StevenMHernandez/pet-bot/network/diagram.png

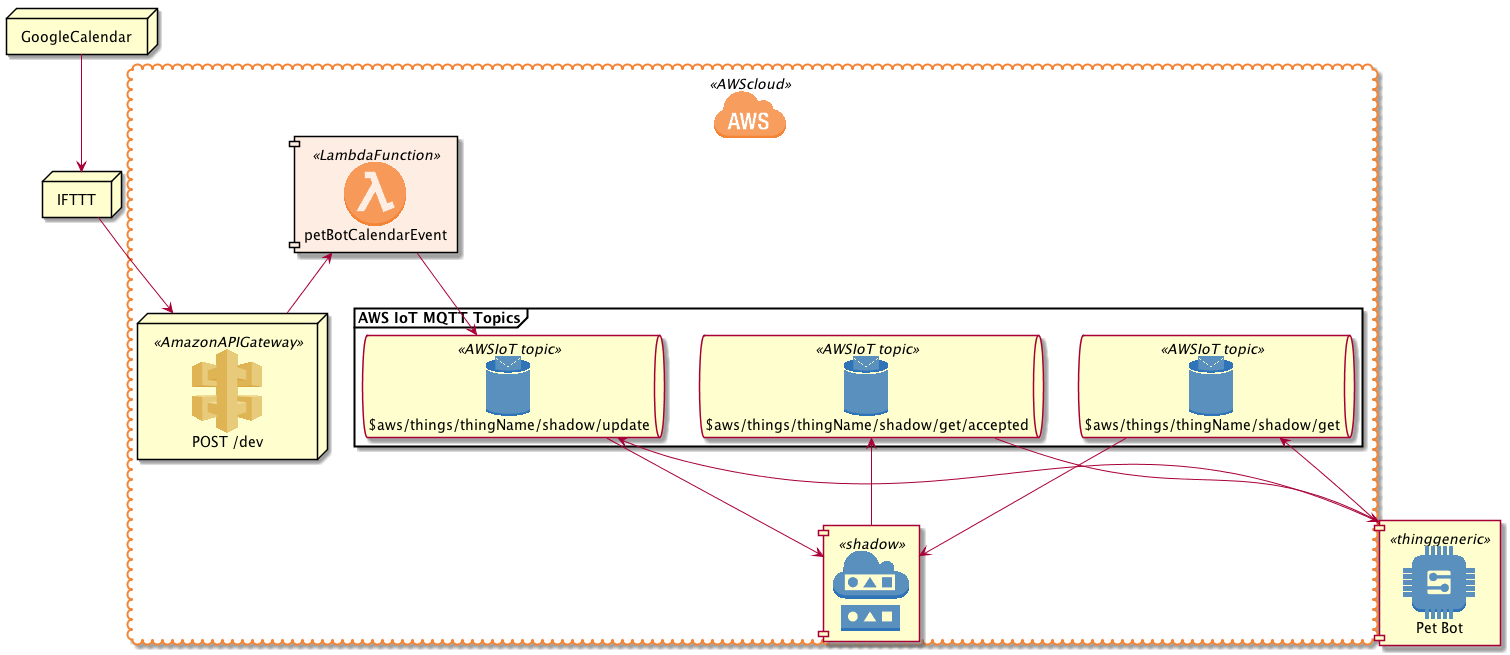
network/diagram.png
