StevenMHernandez/pet-bot/sdcard/CAT01.BMP

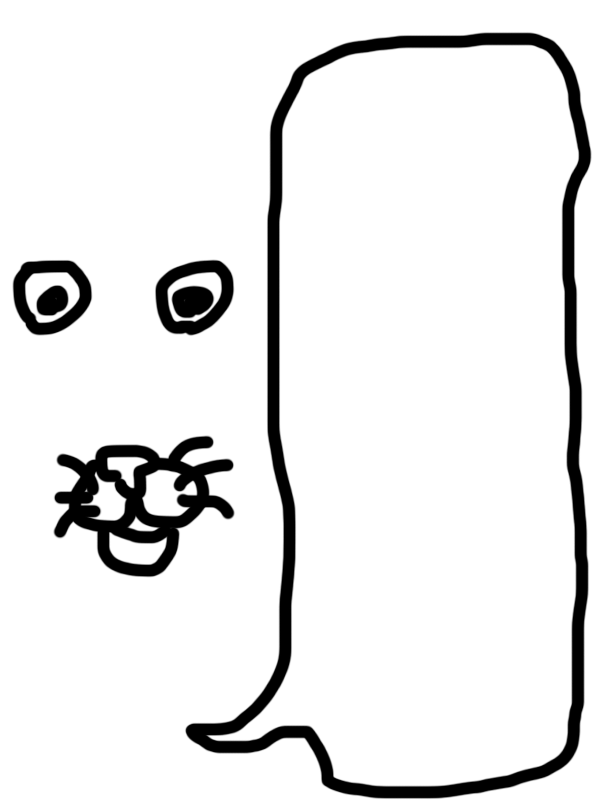
sdcard/CAT01.BMP
