StevenMHernandez/pet-bot/sdcard/CAT10.BMP

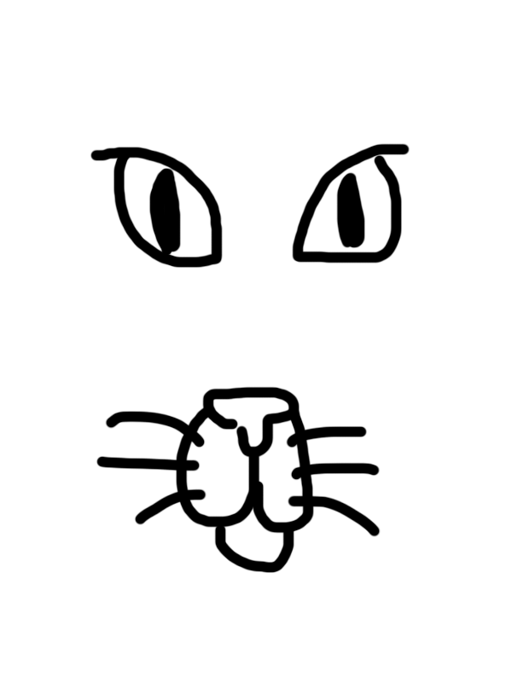
sdcard/CAT10.BMP
