StevenMHernandez/pet-bot/sdcard/DOG00.BMP

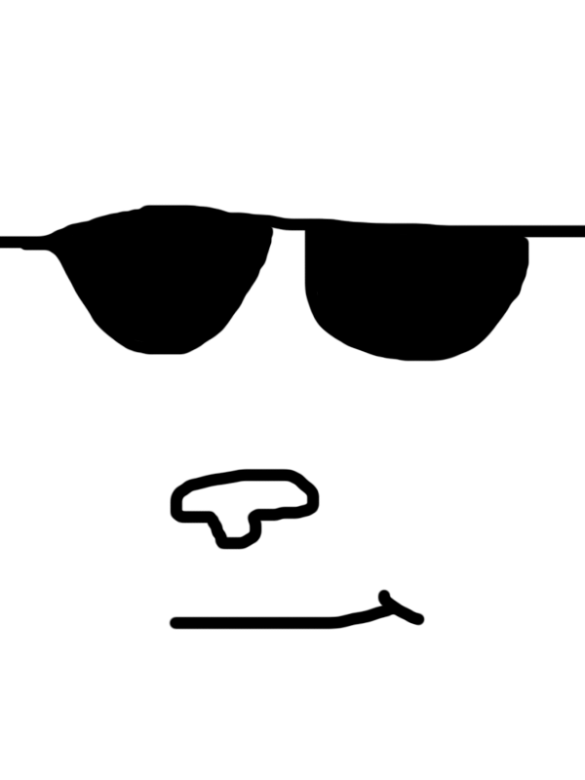
sdcard/DOG00.BMP
