StevenMHernandez/pet-bot/sdcard/DOG01.BMP

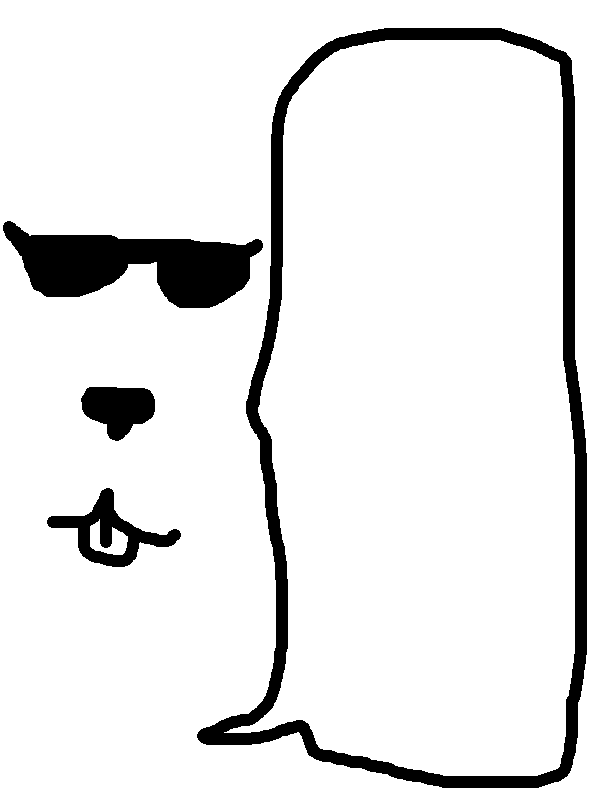
sdcard/DOG01.BMP
