StevenMHernandez/pet-bot/sdcard/DOG10.BMP

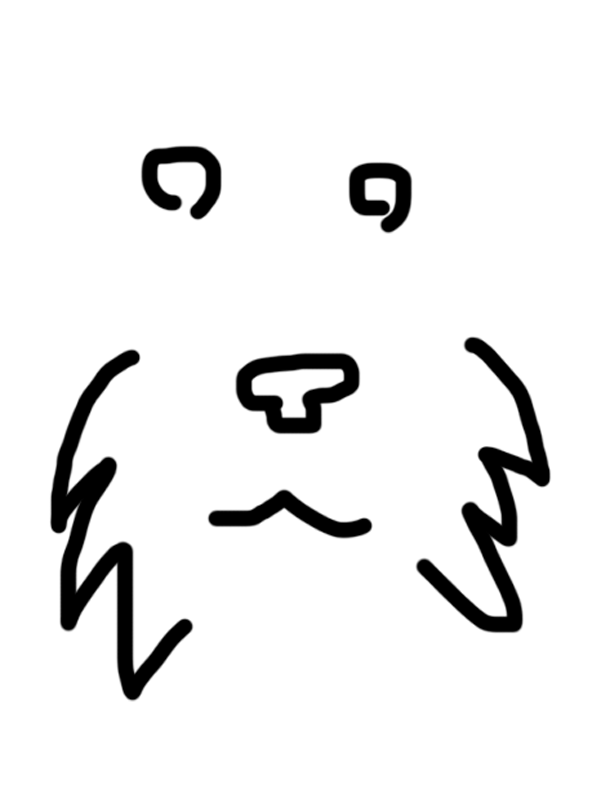
sdcard/DOG10.BMP
