StevenMHernandez/pet-bot/sdcard/DOG11.BMP

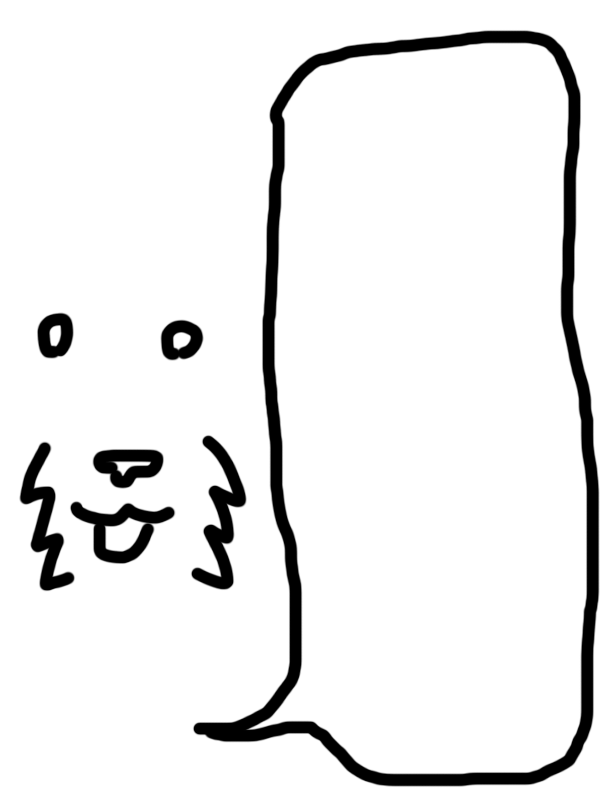
sdcard/DOG11.BMP
