StevenMHernandez/pet-bot/sdcard/DOG21.BMP

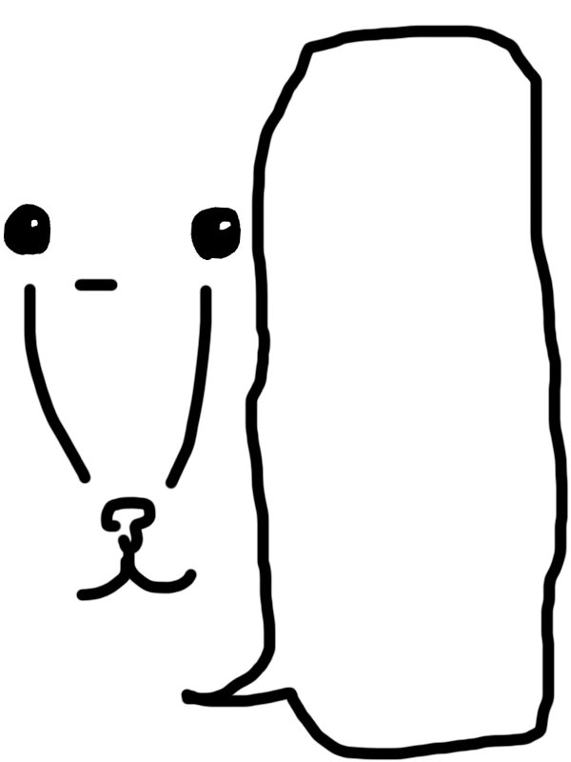
sdcard/DOG21.BMP
