StevenMHernandez/pet-bot/sdcard/RAN00.BMP

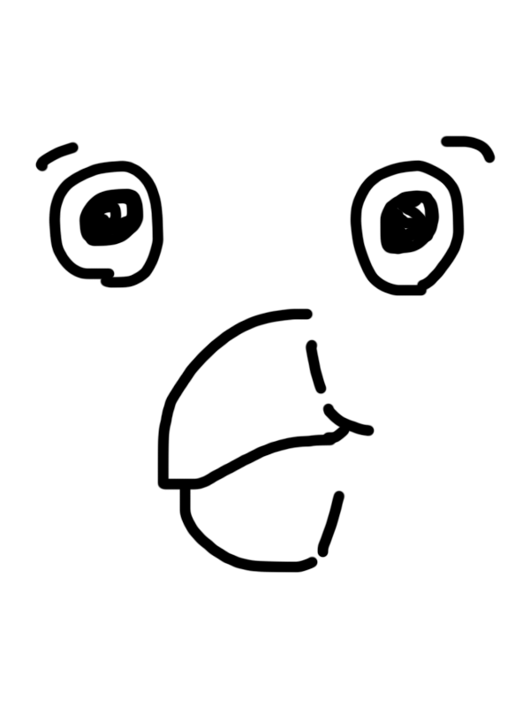
sdcard/RAN00.BMP
