StevenMHernandez/pet-bot/sdcard/RAN01.BMP

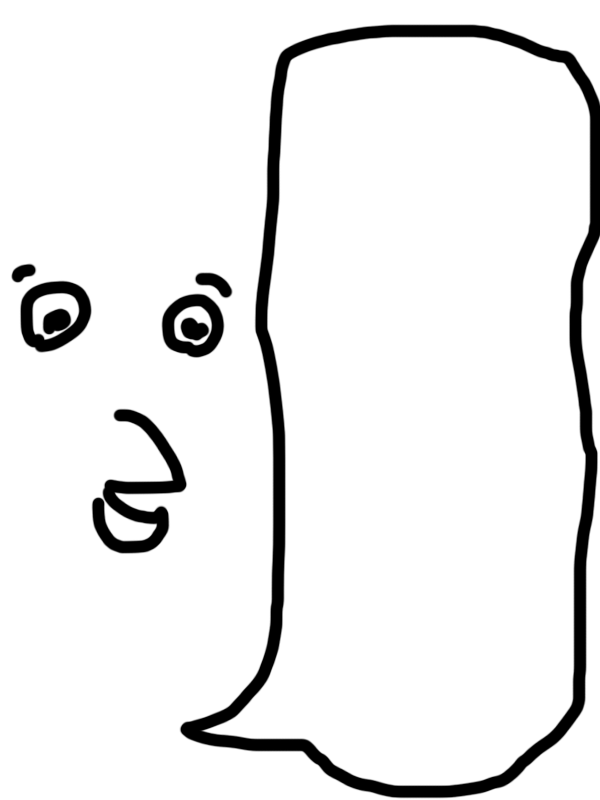
sdcard/RAN01.BMP
