StevenMHernandez/pet-bot/sdcard/RAN10.BMP

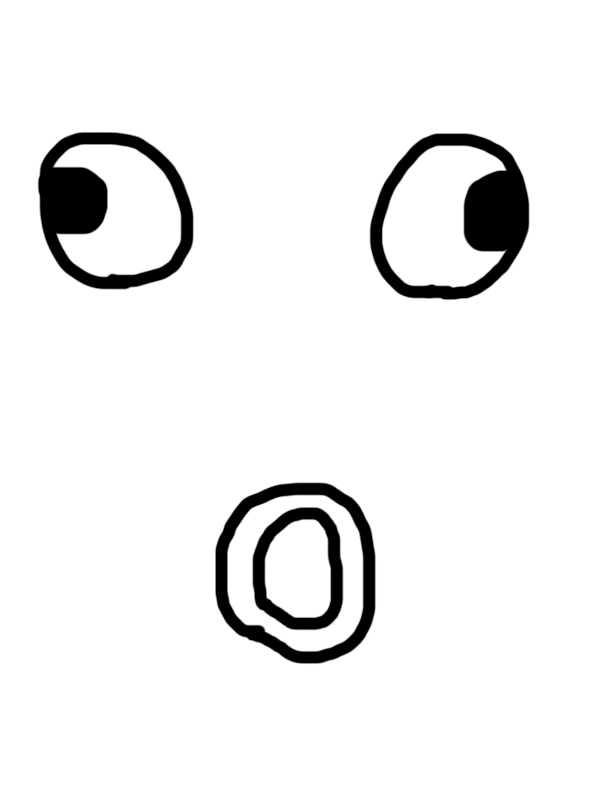
sdcard/RAN10.BMP
