StevenMHernandez/pet-bot/sdcard/RAN20.BMP

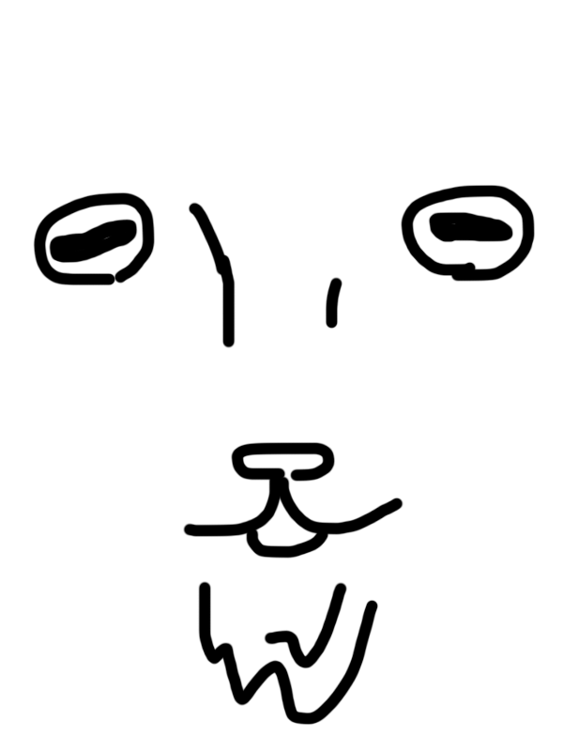
sdcard/RAN20.BMP
