StevenMHernandez/pet-bot/sdcard/RAN21.BMP

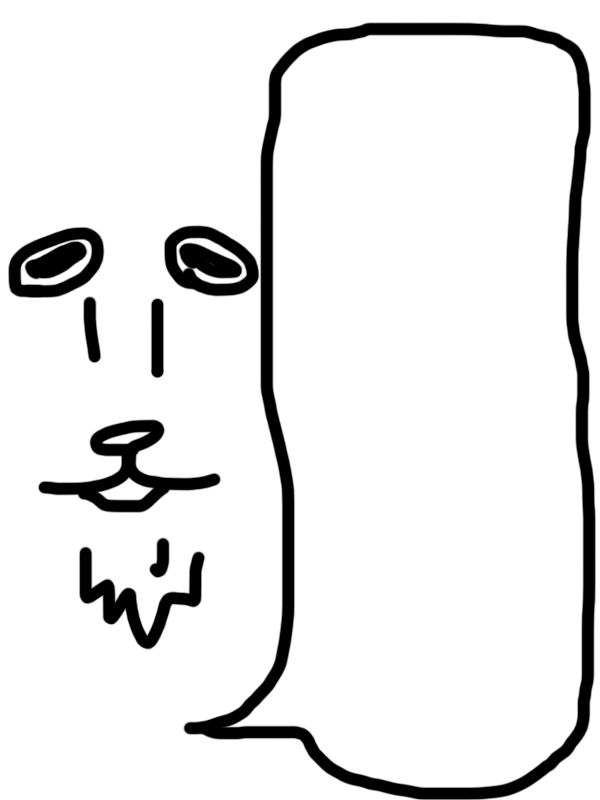
sdcard/RAN21.BMP
